Mario-F/esp-fancontroller/kicad/electric.kicad_sch

## KiCad design kicad/electric.kicad_sch (2023-08-06)

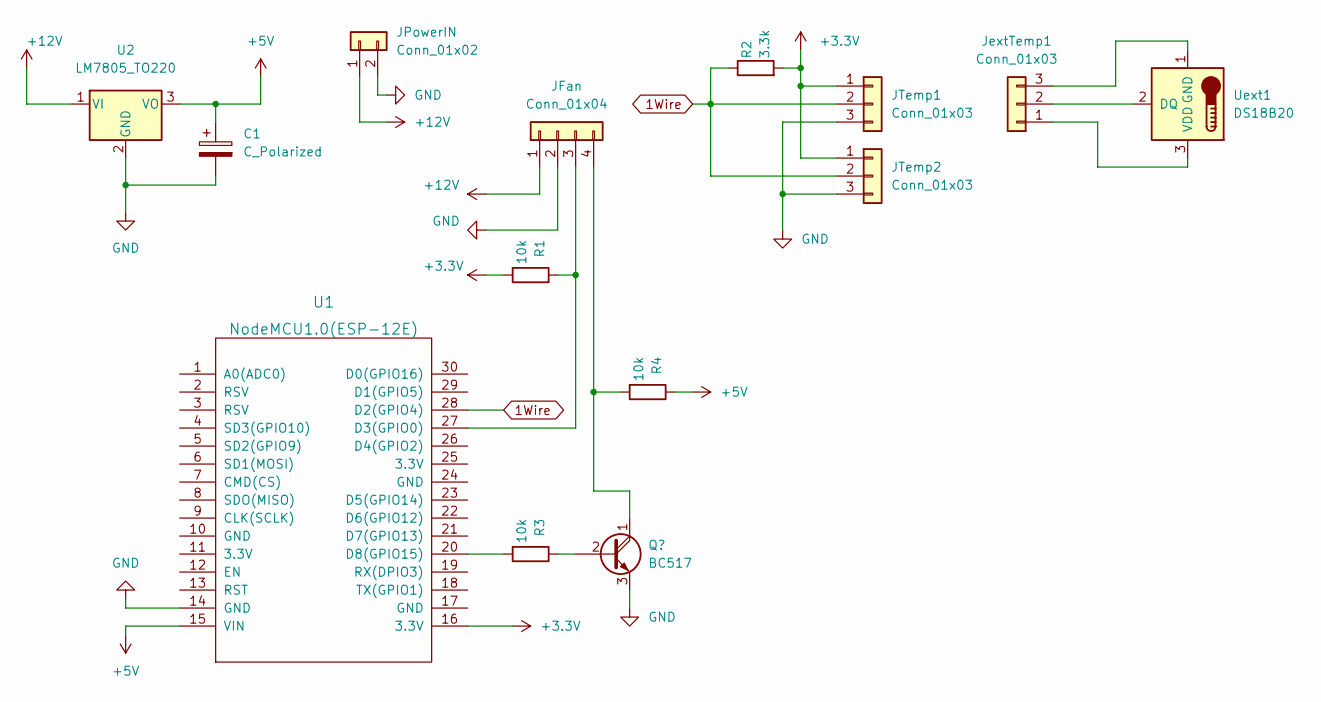
[picture p2: schematic electric.kicad_sch]

Parts:
C1: C_Polarized
JFan: Conn_01x04
JPowerIN: Conn_01x02
JTemp1, JTemp2: Conn_01x03
JextTemp1: Conn_01x03
R1, R3, R4: 10k
R2: 3.3k
U1: NodeMCU1.0(ESP-12E)
U2: LM7805_TO220; TO-220-3_Vertical
Uext1: DS18B20; TO-92_Inline

Connections:
1Wire: JTemp1.2, JTemp2.2, R2.1, U1.28 (D2(GPIO4))
unnamed: C1.1, U2.3 (VO)
unnamed: C1.2, U2.2 (GND)
unnamed: JFan.3, R1.1, U1.27 (D3(GPIO0))
unnamed: JFan.4, R4.2
unnamed: JTemp1.1, JTemp2.1, R2.2
unnamed: JTemp1.3, JTemp2.3
unnamed: JextTemp1.1, Uext1.3 (VDD)
unnamed: JextTemp1.2, Uext1.2 (DQ)
unnamed: JextTemp1.3, Uext1.1 (GND)
unnamed: R3.2, U1.20 (D8(GPIO15))
